GLUD/real-parking/hardware/sensor-isla2/src/sensor-isla.ino

/*  ----------------------------------------------------------------
    http://www.prometec.net/duplex-nrf2401
    Prog_79B_Emisor

    Usando un NRF2401 para comunicar dos Arduinos en modo Duplex
    Programa Emisor:
   --------------------------------------------------------------------
 */

/**
  * Dependencias módulo RF
  */
#include "RF24.h"
#include "nRF24L01.h"
#include <SPI.h>
/*Fin*/

/**
 * Variables Módulo RF
 */
RF24 radio(9, 10);
const uint64_t pipes[2] = {0xF0F0F0F0E1LL,
                           0xF0F0F0F0D2LL}; // LongLong = 64 bits.
/*Fin*/

/**
 * Variable pulsador
 */
byte pulsadorPin = 7;
volatile byte pulsadorEstado = 0;
/*Fin*/

void setup(void) {
  configSerial();
  configRF();
  configPulsador();
}

void configSerial() { Serial.begin(9600); }

void configRF() {
  pinMode(10, OUTPUT);
  radio.begin();

  radio.setRetries(15, 15); // Maximos reintentos
  // radio.setPayloadSize(8);   // Reduce el payload de 32 si tienes problemas

  // Open pipes to other nodes for communication
  radio.openWritingPipe(pipes[0]);
  radio.openReadingPipe(1, pipes[1]);
}

void configPulsador(){
  pinMode(pulsadorPin, INPUT_PULLUP);
}

void loop(void) {
  enviarDatoRF();
  sensarPulsador();
  delay(1000);
}

void enviarDatoRF() {
  radio.stopListening(); // Paramos la escucha para poder hablar
  char idIsla = 2;
  //char estado = 0;
  char msg[2] = {idIsla, pulsadorEstado};
  // unsigned long time = millis();
  Serial.print("Enviando  ");
  Serial.print((int)msg[0]);
  Serial.print(",");
  Serial.println((int)msg[1]);
  // bool ok = radio.write(&time, sizeof(unsigned long));
  bool ok = radio.write(msg, 2);

  if (ok) {
    Serial.println("ok...");
  } else {
    Serial.println("failed");
  }

  radio.startListening(); // Volvemos a la escucha
  //
  // unsigned long started_waiting_at = millis();
  // bool timeout = false;
  // while (!radio.available() && !timeout) { // Esperasmos repsuesta hasta
  // 200ms
  //   if (millis() - started_waiting_at > 200) {
  //     timeout = true;
  //   }
  // }
  //
  // if (timeout) {
  //   Serial.println("FailedEstado, response timed out");
  // } else { // Leemos el mensaje recibido
  //   char got_isla[2];
  //   radio.read(&got_isla, 2);
  //
  //   Serial.print("Respuesta = ");
  //   Serial.print((int)got_isla[0]);
  //   Serial.println((int)got_isla[1]);
  // }
}

void sensarPulsador(){
  boolean val = digitalRead(pulsadorPin);   // read the input pin
  if(val == HIGH){
    pulsadorEstado = 0;
  } else {
    pulsadorEstado = 1;
  }
  //Serial.println(pulsadorEstado);
}
